bababooex/STM8_TV_TRANSMITTER/RFmod_bare_metal/inc/stm8s_delay.h

#ifndef _STM8S_DELAY_H
#define _STM8S_DELAY_H

#include <stdint.h>
#include "stm8s.h"

#define F_CPU 				16000000UL 
#define dly_const			(F_CPU / 16000000.0F) 

void delay_us(unsigned int  value);
void delay_ms(unsigned int  value);
#endif
