bababooex/STM8_TV_TRANSMITTER/RFmod_bare_metal/stm8_interrupt_vector.c

/* stm8_interrupt_vector.c ? Cosmic compiler (STVD) */
extern void _stext(void);

/* Dummy handler for unused interrupts */
@far @interrupt void NonHandledInterrupt(void)
{
    while (1);   // Trap unexpected interrupts
}

/* Your interrupt handlers */
extern @far @interrupt void timer4_isr(void);
extern @far @interrupt void reset_handler(void);
/* Vector Table */
struct interrupt_vector {
    unsigned char interrupt_type;   // 0x82 for interrupt handlers
    @far void *handler;
};

struct interrupt_vector const _vectab[] = {
	{0x82, reset_handler}, /* reset */
	{0x82, NonHandledInterrupt}, /* trap  */
	{0x82, NonHandledInterrupt}, /* irq0  */
	{0x82, NonHandledInterrupt}, /* irq1  */
	{0x82, NonHandledInterrupt}, /* irq2  */
	{0x82, NonHandledInterrupt}, /* irq3  */
	{0x82, NonHandledInterrupt}, /* irq4  */
	{0x82, NonHandledInterrupt}, /* irq5  */
	{0x82, NonHandledInterrupt}, /* irq6  */
	{0x82, NonHandledInterrupt}, /* irq7  */
	{0x82, NonHandledInterrupt}, /* irq8  */
	{0x82, NonHandledInterrupt}, /* irq9  */
	{0x82, NonHandledInterrupt}, /* irq10 */
	{0x82, NonHandledInterrupt}, /* irq11 */
	{0x82, NonHandledInterrupt}, /* irq12 */
	{0x82, NonHandledInterrupt}, /* irq13 */
	{0x82, NonHandledInterrupt}, /* irq14 */
	{0x82, NonHandledInterrupt}, /* irq15 */
	{0x82, NonHandledInterrupt}, /* irq16 */
	{0x82, NonHandledInterrupt}, /* irq17 */
	{0x82, NonHandledInterrupt}, /* irq18 */
	{0x82, NonHandledInterrupt}, /* irq19 */
	{0x82, NonHandledInterrupt}, /* irq20 */
	{0x82, NonHandledInterrupt}, /* irq21 */
	{0x82, NonHandledInterrupt}, /* irq22 */
	{0x82, timer4_isr,}, /* irq23 */
	{0x82, NonHandledInterrupt}, /* irq24 */
	{0x82, NonHandledInterrupt}, /* irq25 */
	{0x82, NonHandledInterrupt}, /* irq26 */
	{0x82, NonHandledInterrupt}, /* irq27 */
	{0x82, NonHandledInterrupt}, /* irq28 */
	{0x82, NonHandledInterrupt}, /* irq29 */
};
